ProjectKitchen/Drone/Software/README.txt

FC-Kommunikation:
	Programm zur Kommunikation zwischen Flight-Controller (FC) und Steuer-Mikrocontroller.

FHTW-Drohne:
	Mobiltelefon-Applikation zur Drohnensteuerung.

MultiWii_2_1_HK_Board_V3:
	MultiWii-Programm für den FC.

Steuerung:
	Programm zur FC-Steuerung mit Hilfe des Steuer-Mikrocontrollers.
