ProjectKitchen/Drone/Electronics/Driver/Driver.pdf

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

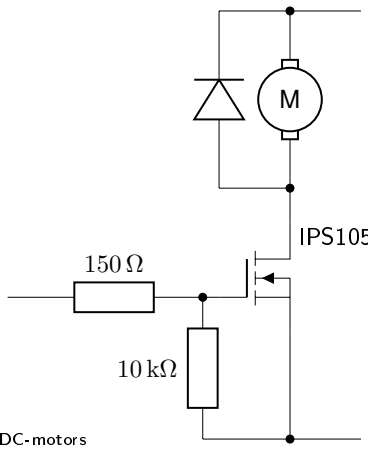
[picture p31: figure]
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
